HIAndris/2Dwith2Eyes/resources/.stl/elemtarto_5.stl

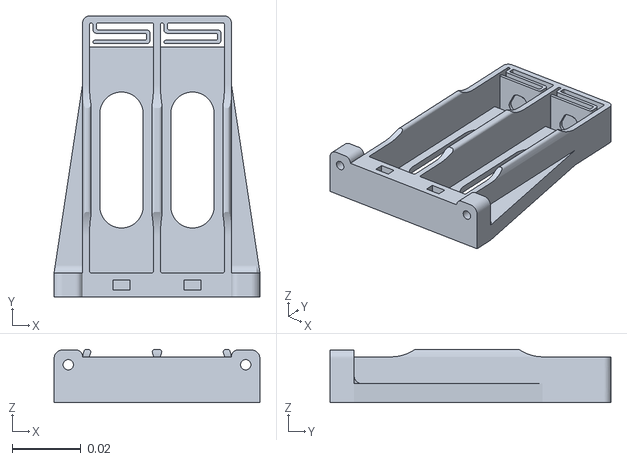
[picture p15: CAD file, 2025-05-28]
resources/.stl/elemtarto_5.stl
0.0598 x 0.0815 x 0.0155
