HIAndris/2Dwith2Eyes/resources/.stl/nyak_tarto_bal_2.stl

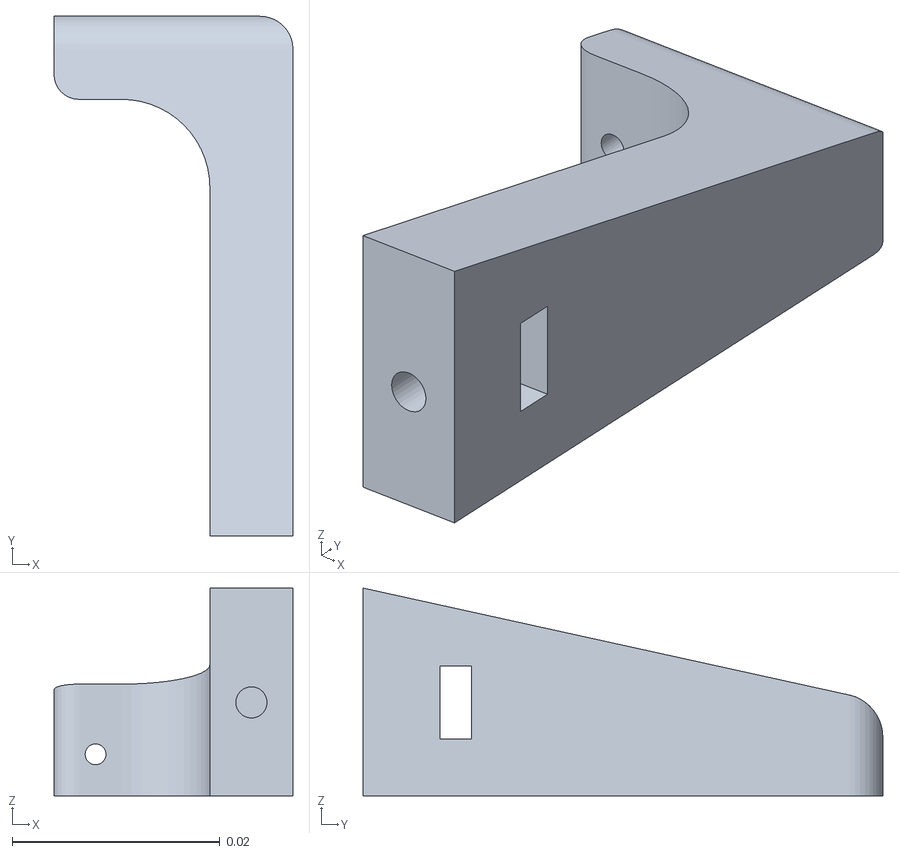
[picture p16: CAD file, 2025-05-25]
resources/.stl/nyak_tarto_bal_2.stl
0.023 x 0.05 x 0.02
