HIAndris/2Dwith2Eyes/resources/.stl/elemtarto_4.stl

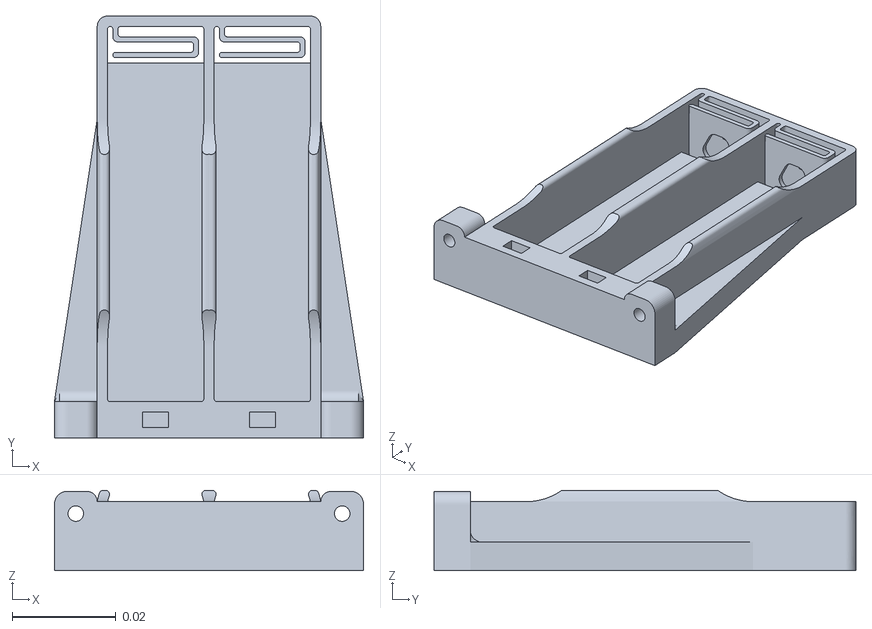
[picture p17: CAD file, 2025-05-25]
resources/.stl/elemtarto_4.stl
0.0598 x 0.0815 x 0.0155
