HIAndris/2Dwith2Eyes/resources/.stl/nyak_vaz.stl

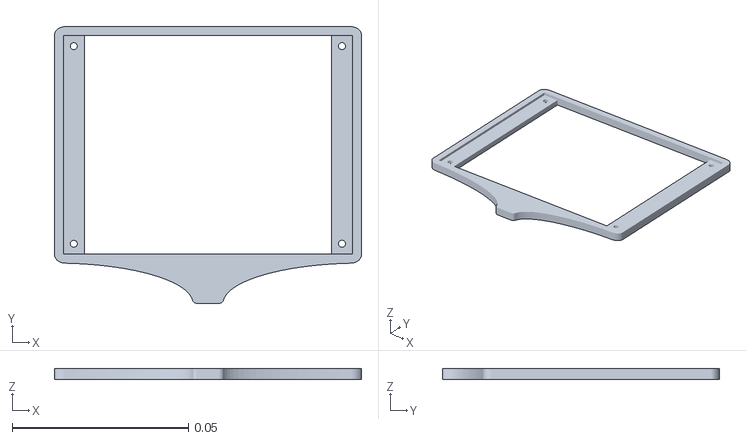
[picture p18: CAD file, 2025-05-25]
resources/.stl/nyak_vaz.stl
0.087 x 0.0784 x 0.003
