HIAndris/2Dwith2Eyes/resources/.stl/alvaz_elulso.stl

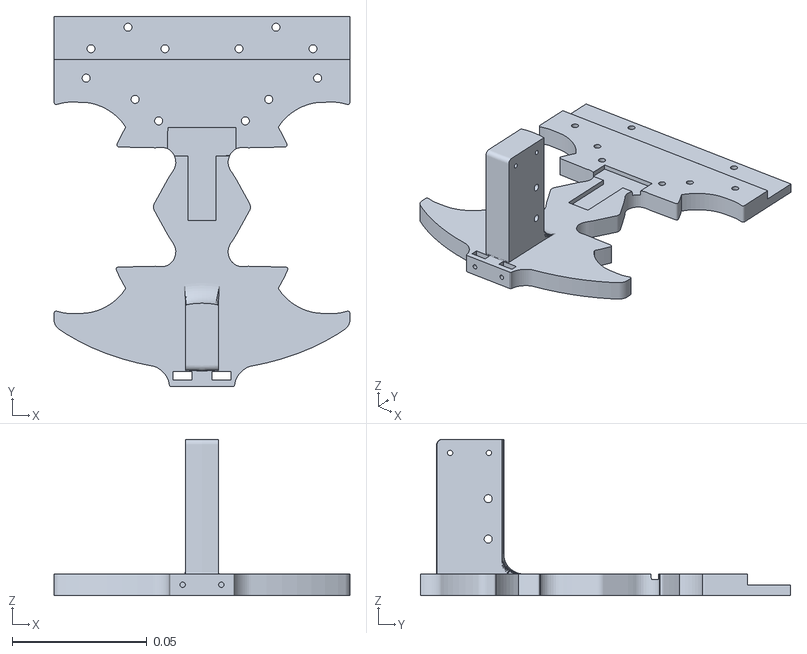
[picture p19: CAD file, 2025-05-25]
resources/.stl/alvaz_elulso.stl
0.11 x 0.138 x 0.058
