HIAndris/2Dwith2Eyes/resources/.stl/kanyarodo_motor_tartokeret_2.stl

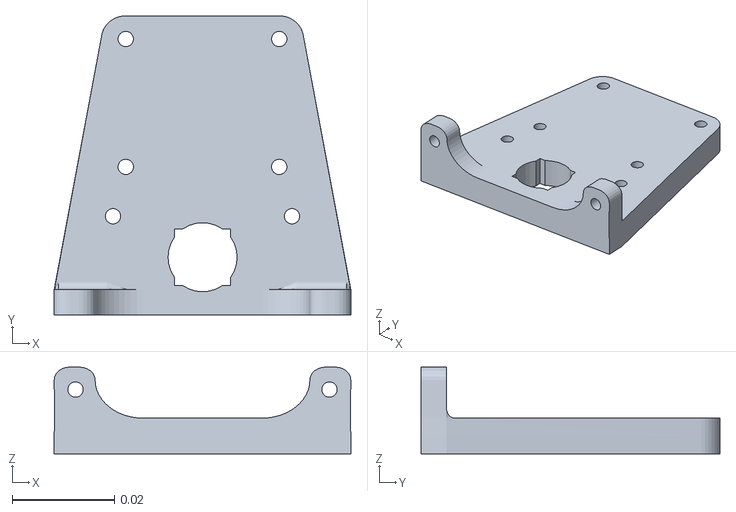
[picture p20: CAD file, 2025-05-25]
resources/.stl/kanyarodo_motor_tartokeret_2.stl
0.058 x 0.0585 x 0.017
