HIAndris/2Dwith2Eyes/resources/.stl/kanyarodo_motor_tartokeret.stl

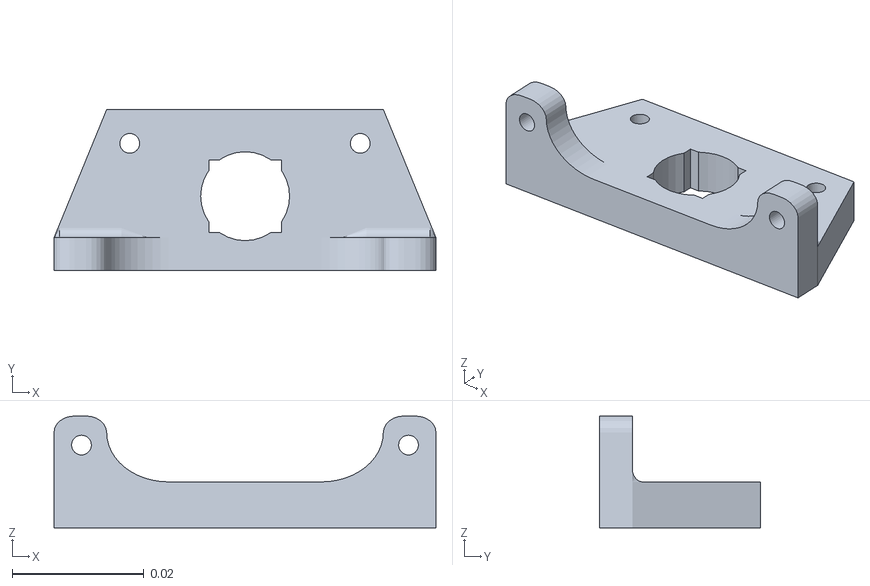
[picture p21: CAD file, 2025-05-18]
resources/.stl/kanyarodo_motor_tartokeret.stl
0.058 x 0.0245 x 0.017
