HIAndris/2Dwith2Eyes/resources/.stl/elemtarto_3.stl

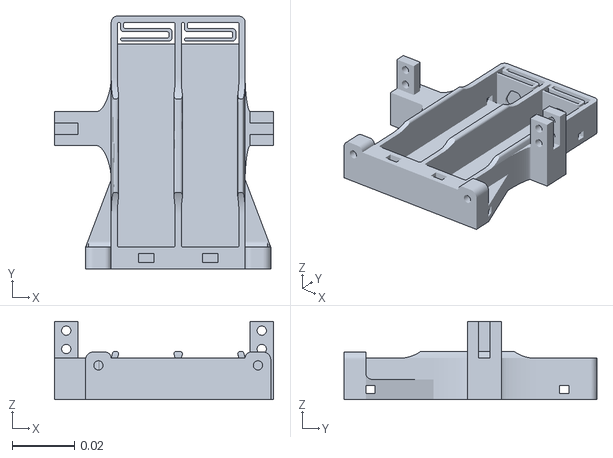
[picture p22: CAD file, 2025-05-18]
resources/.stl/elemtarto_3.stl
0.0706 x 0.0815 x 0.0252
