HIAndris/2Dwith2Eyes/resources/.stl/elemtarto.stl

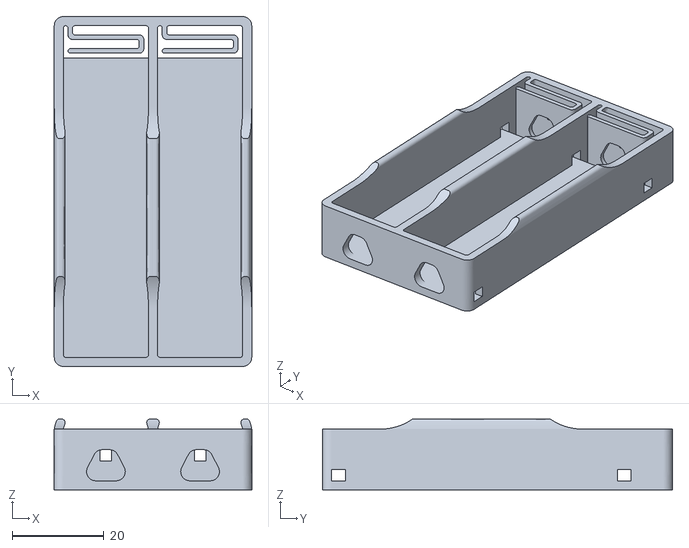
[picture p23: CAD file, 2025-05-18]
resources/.stl/elemtarto.stl
43.0 x 76.2 x 15.5
