HIAndris/2Dwith2Eyes/resources/.stl/elemtarto_2.stl

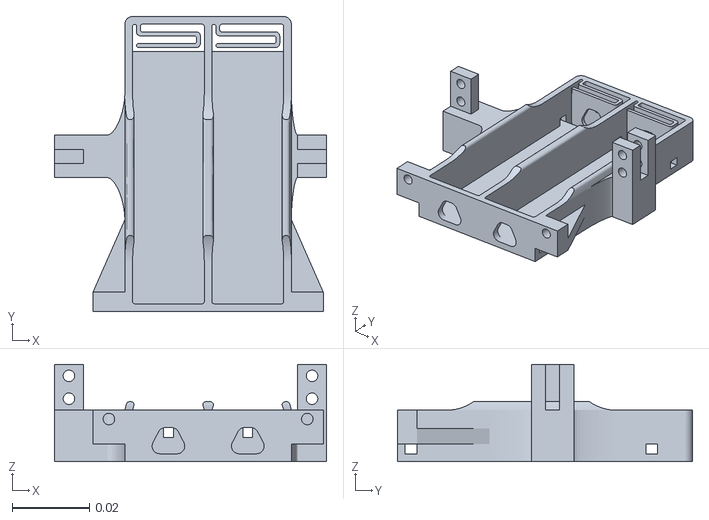
[picture p24: CAD file, 2025-05-18]
resources/.stl/elemtarto_2.stl
0.0706 x 0.0765 x 0.0252
