HIAndris/2Dwith2Eyes/resources/.stl/alvaz_hatso.stl

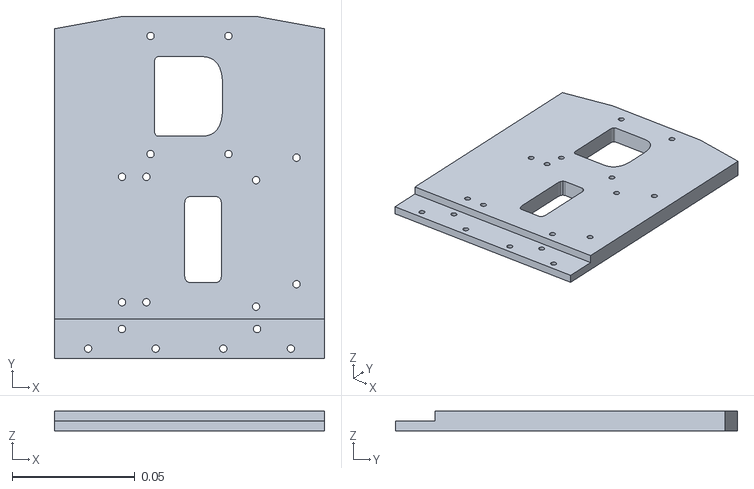
[picture p25: CAD file, 2025-05-17]
resources/.stl/alvaz_hatso.stl
0.11 x 0.139 x 0.008
