HIAndris/2Dwith2Eyes/resources/.stl/hajtotengely_axle_atalakito_2.stl

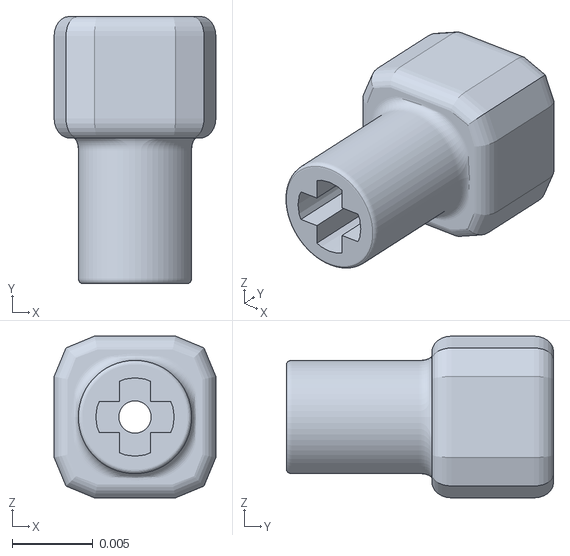
[picture p26: CAD file, 2025-05-10]
resources/.stl/hajtotengely_axle_atalakito_2.stl
0.01 x 0.0165 x 0.01
