HIAndris/2Dwith2Eyes/resources/.stl/hajtotengely_axle_atalakito.stl

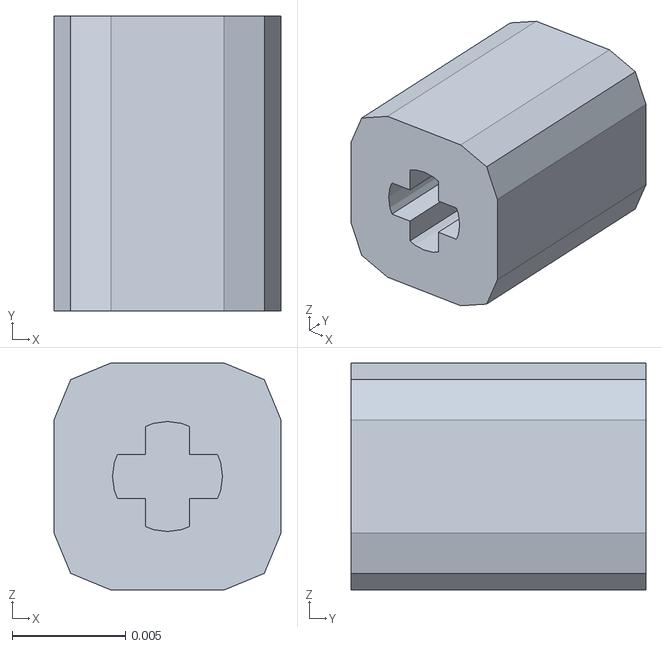
[picture p27: CAD file, 2025-05-08]
resources/.stl/hajtotengely_axle_atalakito.stl
0.01 x 0.013 x 0.01
