HIAndris/2Dwith2Eyes/resources/.stl/hajtomotor_tartokeret_2.stl

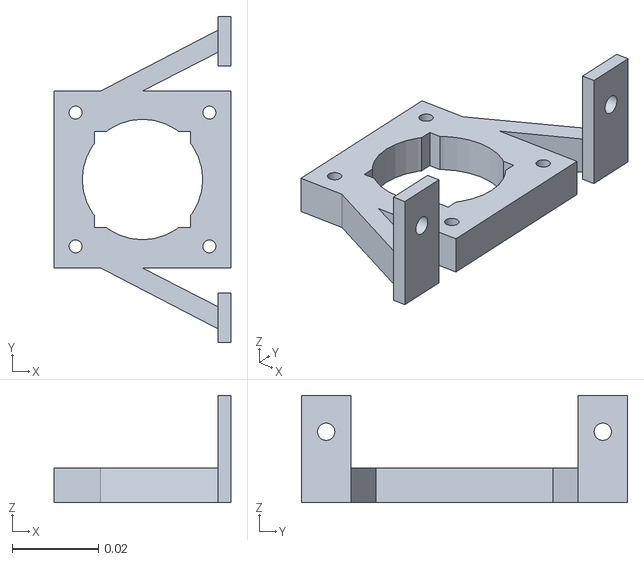
[picture p28: CAD file, 2025-05-08]
resources/.stl/hajtomotor_tartokeret_2.stl
0.041 x 0.0756 x 0.0248
