HIAndris/2Dwith2Eyes/resources/.stl/kormanytengely.stl

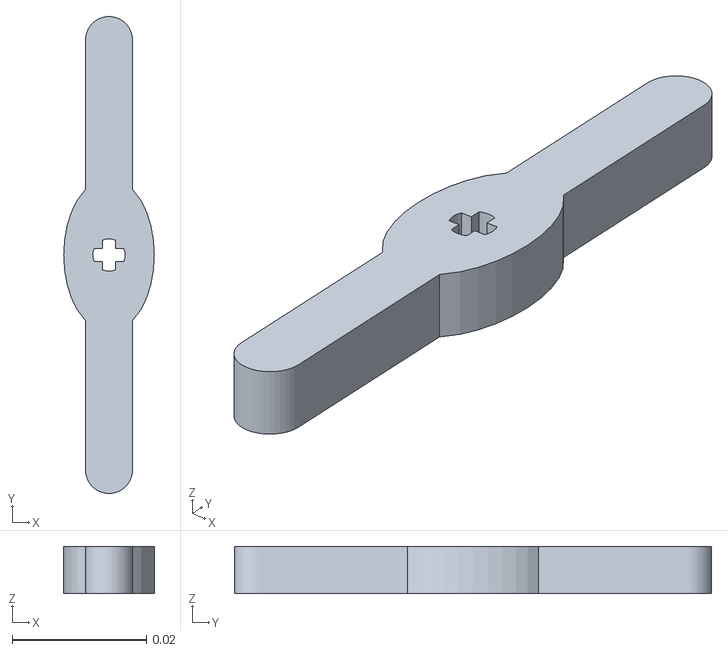
[picture p29: CAD file, 2025-05-08]
resources/.stl/kormanytengely.stl
0.0135 x 0.071 x 0.007
