HIAndris/2Dwith2Eyes/resources/.stl/hajtomotor_tartokeret.stl

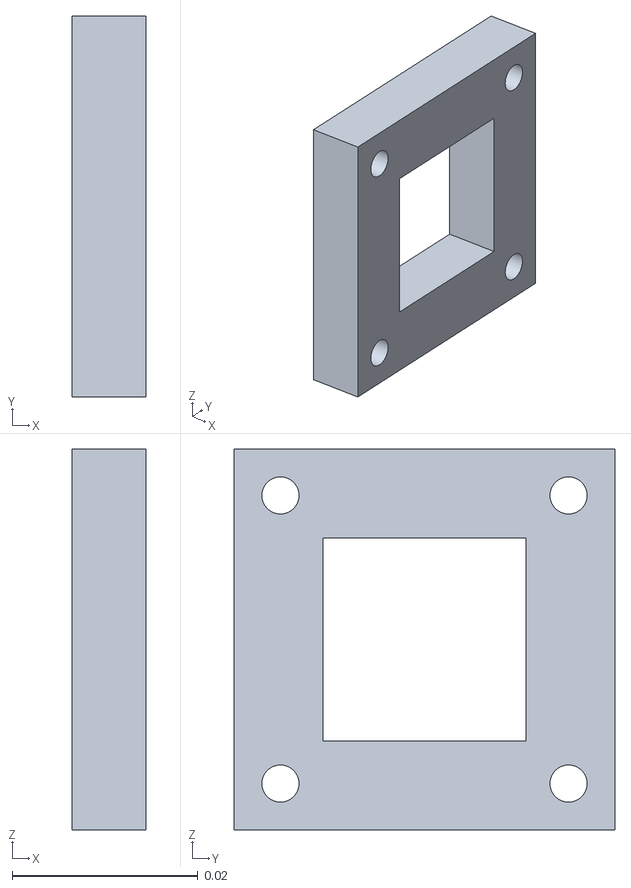
[picture p30: CAD file, 2025-05-08]
resources/.stl/hajtomotor_tartokeret.stl
0.008 x 0.041 x 0.041
