HIAndris/2Dwith2Eyes/src/controller.hpp

#ifndef CONTROLLER_HPP
#define CONTROLLER_HPP

#include "config.hpp"
//#include "status.hpp"
#include "collector.hpp"
#include "motor.hpp"

typedef enum {
    TCH_READY,
    TCH_SHORT,
    TCH_LONG,
    TCH_BUSY
} touch_type_t;

//extern Status status;
extern Collector collector;

class Controller {
  public:
    Controller();

    void touch(touch_type_t touch_type);
    touch_type_t get_touch_type();
    void main();
  
  private:
    touch_type_t touch_state;

    DriveMotor drive_motor;
    SteerMotor steer_motor;

    uint16_t get_distance(uint8_t sensor_num);
};

#endif
